mauntrelio/NodeMCU_door_watcher/data/alarm_0.png

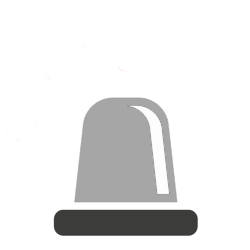
data/alarm_0.png
