mauntrelio/NodeMCU_door_watcher/data/alarm_3.png

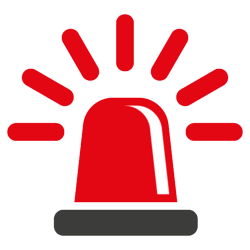
data/alarm_3.png
