mauntrelio/NodeMCU_door_watcher/data/door.png

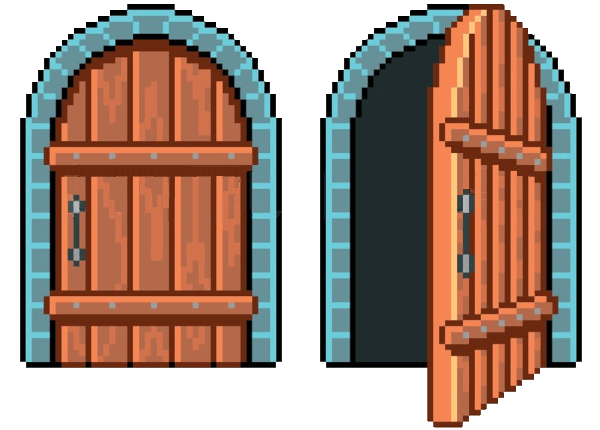
data/door.png
