mauntrelio/NodeMCU_door_watcher/docs/IMG_20180811_153614.jpg

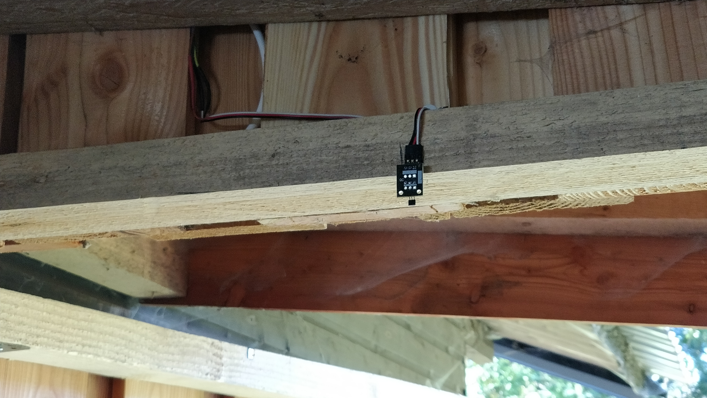
docs/IMG_20180811_153614.jpg
