mauntrelio/NodeMCU_door_watcher/docs/IMG_20180811_153655.jpg

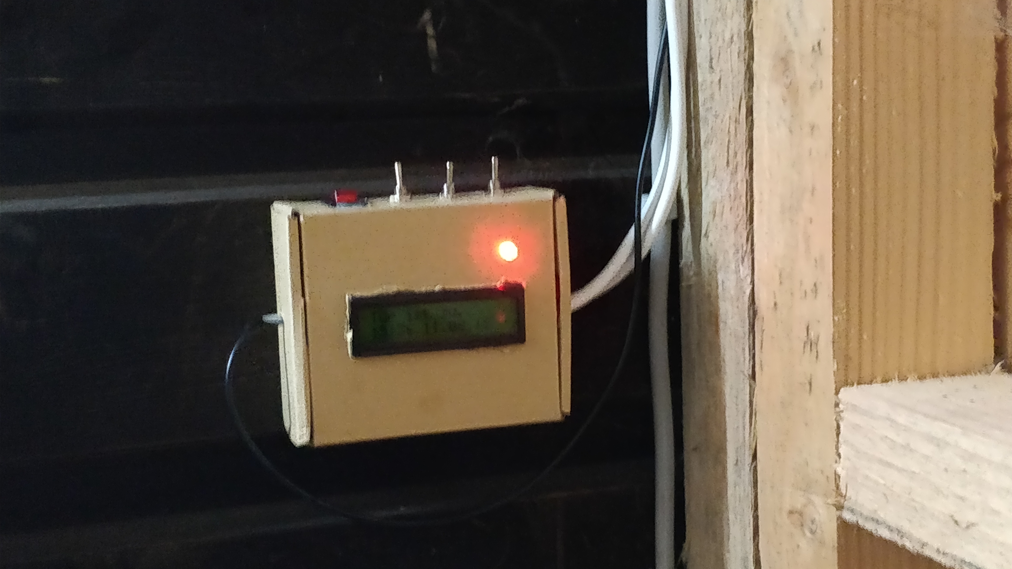
docs/IMG_20180811_153655.jpg
